johnvoipguy/WateefyElectronics/images/node mini headers.png

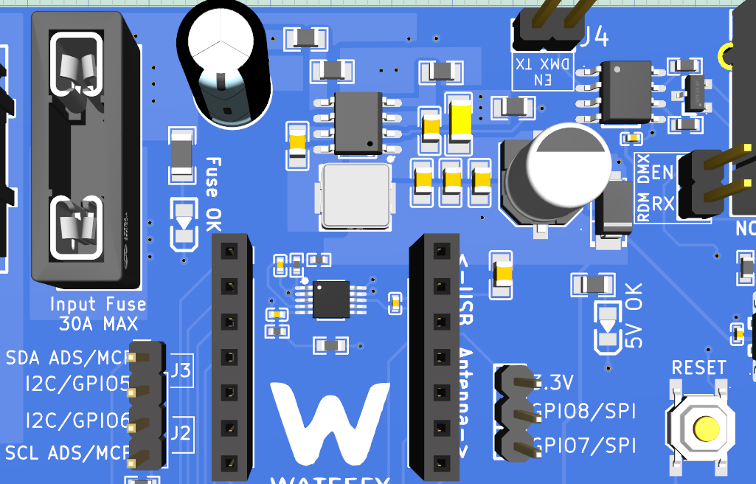
images/node mini headers.png
