johnvoipguy/WateefyElectronics/images/Node_Power_4.png

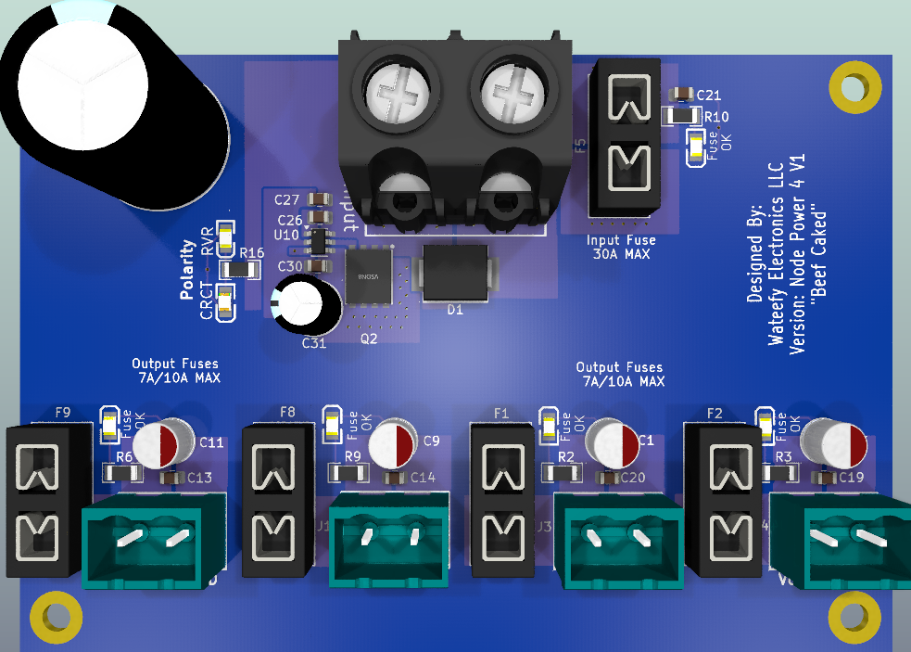
images/Node_Power_4.png
