johnvoipguy/WateefyElectronics/images/Node_Power_8.png

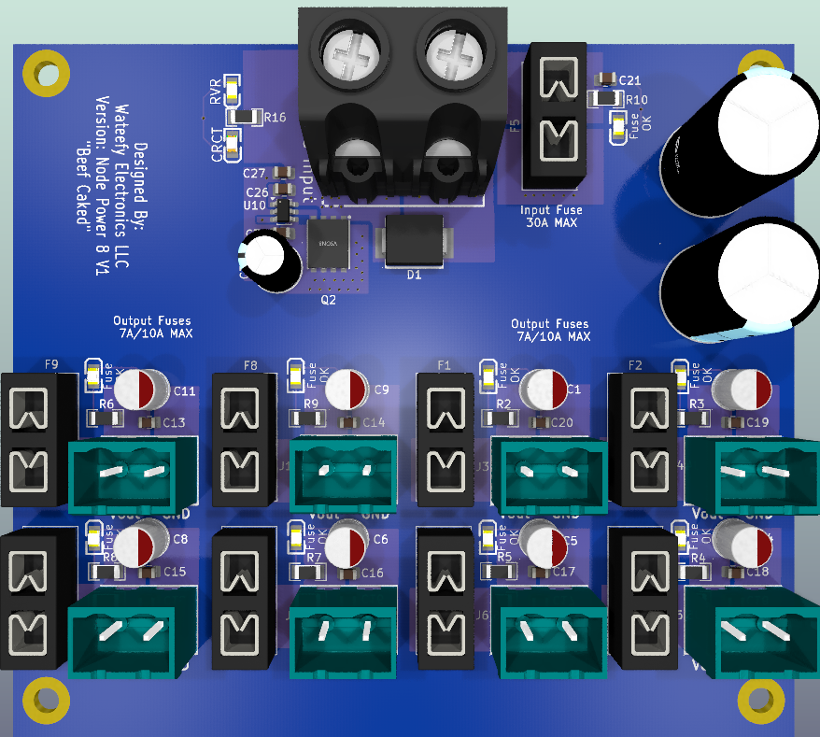
images/Node_Power_8.png
